ShlokVaidya/Super-Ducky/firmware/tusb_config.h

#ifndef _TUSB_CONFIG_H_
#define _TUSB_CONFIG_H_

#define CFG_TUSB_MCU OPT_MCU_RP2040
#define CFG_TUSB_RHPORT0_MODE OPT_MODE_DEVICE

#define CFG_TUD_ENDPOINT0_SIZE 64

#define CFG_TUD_MSC 1
#define CFG_TUD_HID 1

#endif
